SaiDBod/Diya_Neuron/software/docs/images/advanced_settings.png

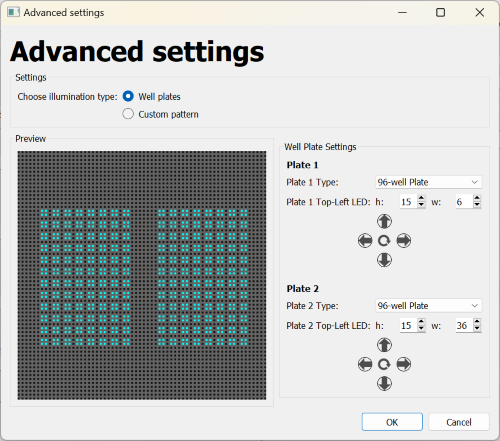
software/docs/images/advanced_settings.png
