SaiDBod/Diya_Neuron/software/docs/images/DIYA_screenshot_labeled.png

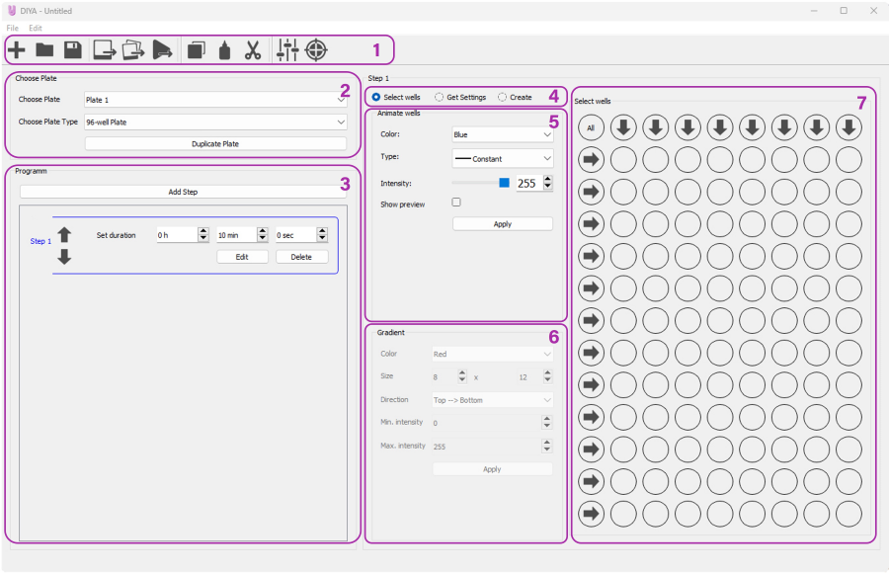
software/docs/images/DIYA_screenshot_labeled.png
