SaiDBod/Diya_Neuron/software/docs/images/parameter_settings_all_options.png

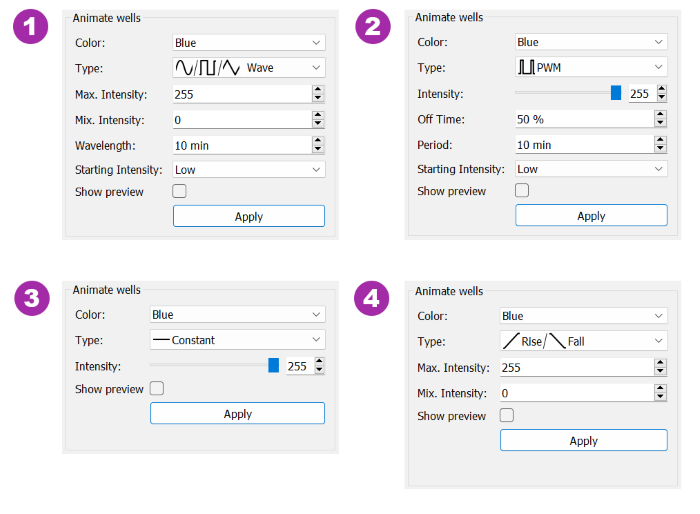
software/docs/images/parameter_settings_all_options.png
