SaiDBod/Diya_Neuron/software/docs/images/preview.png

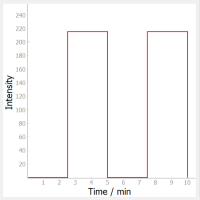
software/docs/images/preview.png
