SaiDBod/Diya_Neuron/software/docs/images/well_information.png

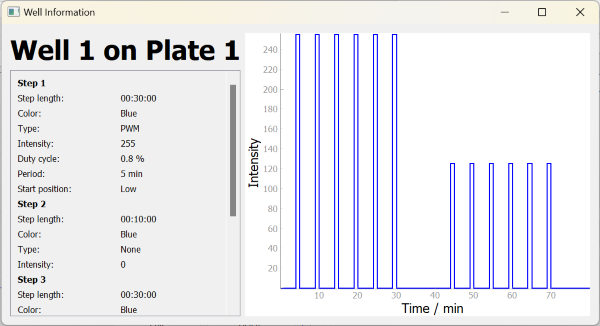
software/docs/images/well_information.png
