SaiDBod/Diya_Neuron/software/calibration/gel_imager_images_for_calibration/red_80_exp_20ms.tif

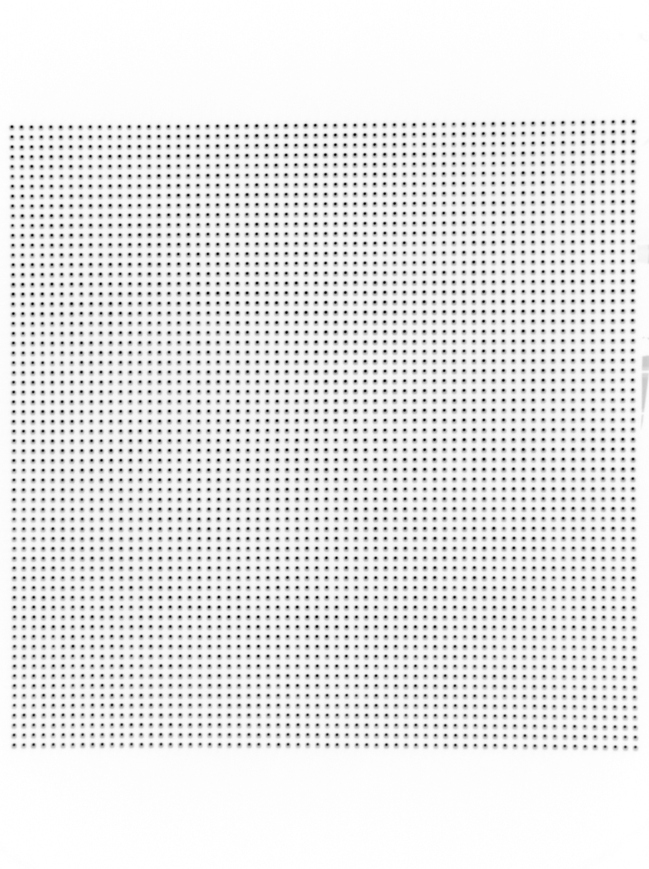
software/calibration/gel_imager_images_for_calibration/red_80_exp_20ms.tif
