SaiDBod/Diya_Neuron/software/docs/images/calibration.png

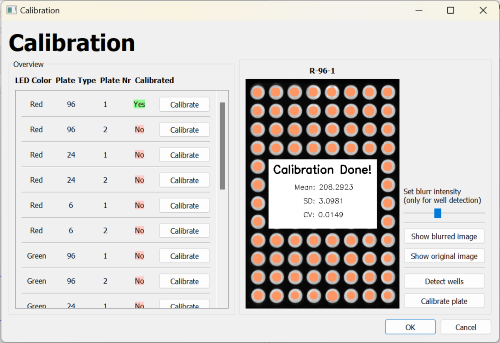
software/docs/images/calibration.png
